kahache7/Pajaros_en_la_nube/Caseta/Fotos/IMG_20210209_124504.jpg

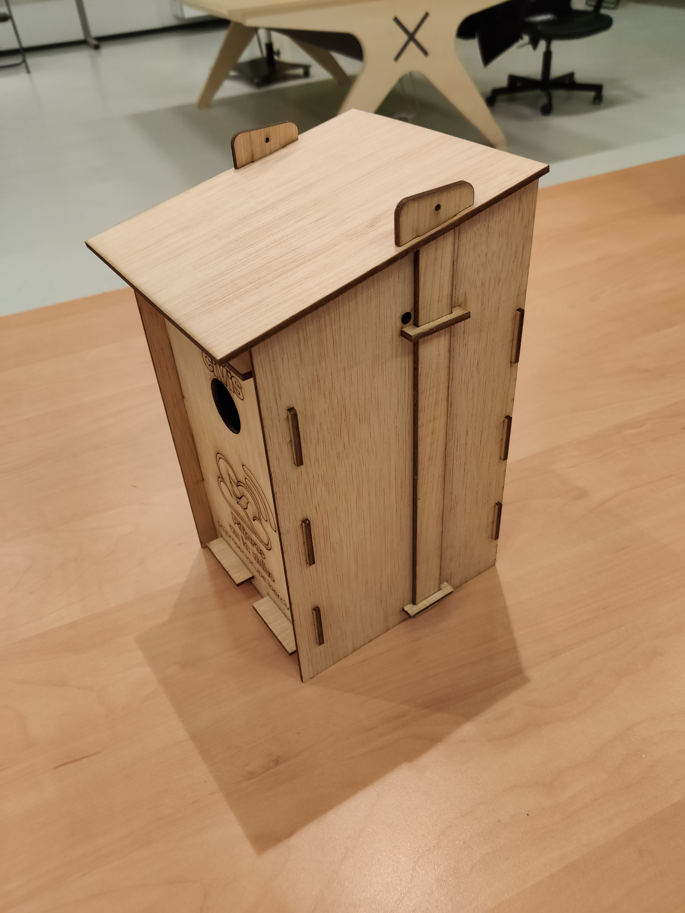
Caseta/Fotos/IMG_20210209_124504.jpg
