kahache7/Pajaros_en_la_nube/Caseta/Fotos/IMG_20210210_171850.jpg

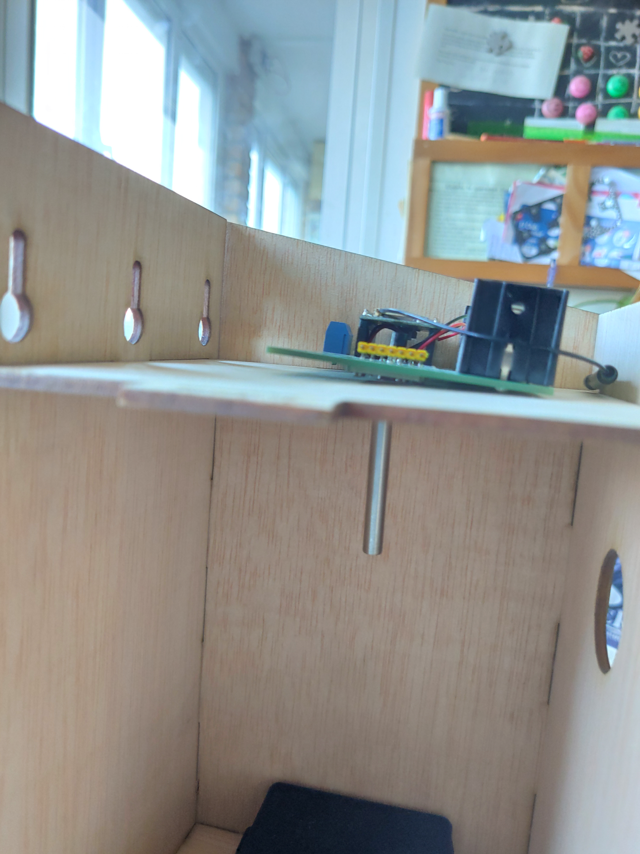
Caseta/Fotos/IMG_20210210_171850.jpg
