kahache7/Pajaros_en_la_nube/Firmware/pajaros_20_21_v1/lora_keys.h

/* ABP para*/
// para simplificar copy paste en TTN
// 896557F8C5726827D3E0D76AF93B4040
// 39D7EF18231A231EF622BE055DB192E1
// birdhouse_05x

uint8_t mynwkSKey[] = { 0x89, 0x65, 0x57, 0xF8, 0xC5, 0x72, 0x68, 0x27, 0xD3, 0xE0, 0xD7, 0x6A, 0xF9, 0x3B, 0x40, 0x40 };
uint8_t myappSKey[] = { 0x39, 0xD7, 0xEF, 0x18, 0x23, 0x1A, 0x23, 0x1E, 0xF6, 0x22, 0xBE, 0x05, 0x5D, 0xB1, 0x92, 0xE1 };


//Si vas a mofificar el firmware de una caseta del proyecto 
//  avisa a los organizadores para que te faciliten tu Device Address
//  dentro del proyecto
uint32_t mydevAddr =  ( uint32_t )0xFFFFFFFF; //Device Address (4 bytes)
